camrentm/Rana-Moth-WASD/Shell/Moth Top Left.step

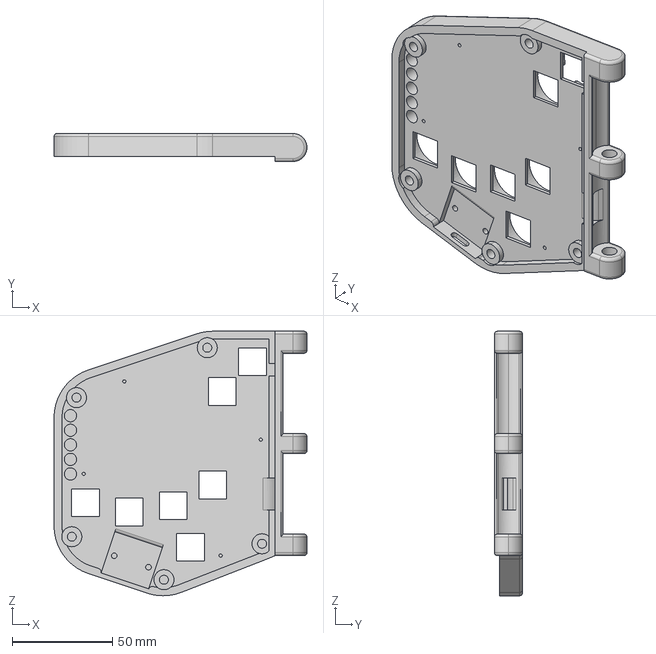
[picture p17: CAD file, 2026-06-16]
Shell/Moth Top Left.step
126.0 x 14.0 x 131.8 mm
QuRB and Reshape
Top Left Moth CTM v19.step
