camrentm/Rana-Moth-WASD/DXF/Left PCB - Holes.dxf

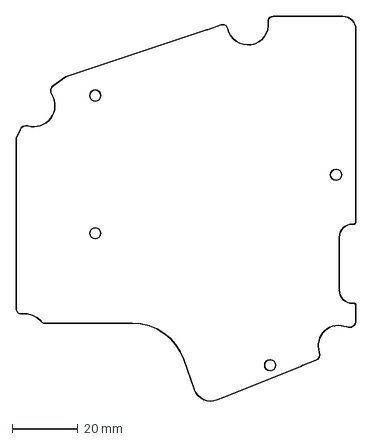
[picture p18: CAD file, 2026-06-16]
DXF/Left PCB - Holes.dxf
103.0 x 116.8 mm
