camrentm/Rana-Moth-WASD/Hinge and Buttons/Hinge Pin.step

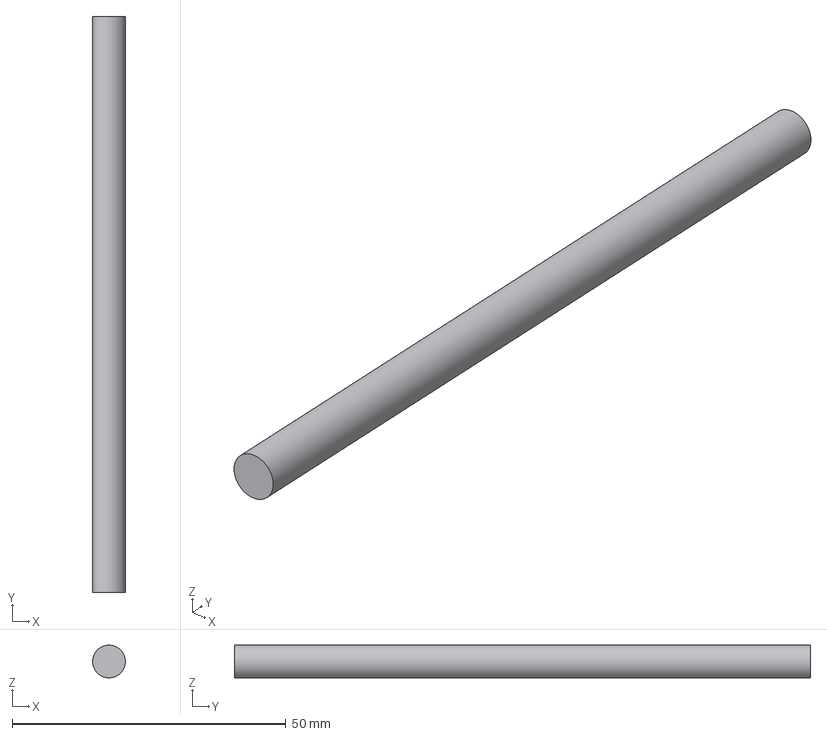
[picture p19: CAD file, 2026-06-16]
Hinge and Buttons/Hinge Pin.step
6.00 x 105.3 x 5.99 mm
