camrentm/Rana-Moth-WASD/DXF/Right PCB - Holes.dxf

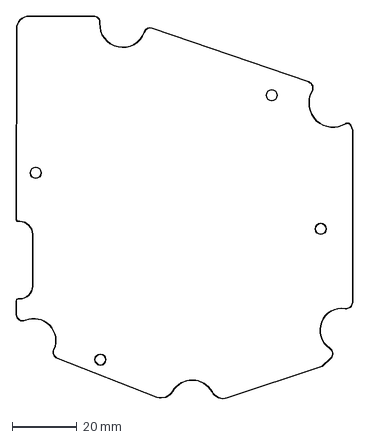
[picture p20: CAD file, 2026-06-16]
DXF/Right PCB - Holes.dxf
104.0 x 118.7 mm
